chukione/RP2040Boy/Arduinoboy/din5.h

#define din5_width 20
#define din5_height 18
static const unsigned char din5_bits[] U8X8_PROGMEM = {
    0xc0, 0x3f, 0x00, 0xf0, 0xff, 0x00, 0xf8, 0xff, 0x01, 0xfc, 0xf9, 0x03,
    0xfc, 0xf9, 0x03, 0x9e, 0x9f, 0x07, 0x9e, 0x9f, 0x07, 0xfe, 0xff, 0x07,
    0xe7, 0x7f, 0x0e, 0xe7, 0x7f, 0x0e, 0xfe, 0xff, 0x07, 0xfe, 0xff, 0x07,
    0xfe, 0xff, 0x07, 0xfc, 0xff, 0x03, 0xfc, 0xff, 0x03, 0xf8, 0xff, 0x01,
    0xf0, 0xf9, 0x00, 0xe0, 0x70, 0x00};
