chukione/RP2040Boy/Arduinoboy/usb.h

#define usb_width 38
#define usb_height 18
static const unsigned char usb_bits[] U8X8_PROGMEM = {
    0x00, 0xf8, 0xff, 0x00, 0x00, 0x00, 0xfc, 0xff, 0xfe, 0x3f, 0x00, 0xfe,
    0xff, 0xfe, 0x3f, 0x00, 0xff, 0xff, 0xfe, 0x3f, 0xe0, 0xff, 0xff, 0x3e,
    0x3e, 0xf0, 0xff, 0xff, 0x3e, 0x3e, 0xff, 0xff, 0xff, 0x3e, 0x3e, 0xff,
    0xff, 0xff, 0x3e, 0x3e, 0xff, 0xff, 0xff, 0xfe, 0x3f, 0xff, 0xff, 0xff,
    0xfe, 0x3f, 0xff, 0xff, 0xff, 0x3e, 0x3e, 0xff, 0xff, 0xff, 0x3e, 0x3e,
    0xf0, 0xff, 0xff, 0x3e, 0x3e, 0xe0, 0xff, 0xff, 0x3e, 0x3e, 0x00, 0xff,
    0xff, 0xfe, 0x3f, 0x00, 0xfe, 0xff, 0xfe, 0x3f, 0x00, 0xfc, 0xff, 0xfe,
    0x3f, 0x00, 0xf8, 0xff, 0x00, 0x00};
